buzali/SuperListas/Firmware/SL App/LCD.c

/*********************************************************************
 *
 *                  LCD.c
 * 
*********************************************************************/

#include "HardwareProfile.h"
#include "Dogm/utility/dogm128.h"
#include <libpic30.h>
#include "LCD.h"
#include <stdlib.h>

//SuperListas Logo
const unsigned char logo_win [] = {
0x00, 0x00, 0x00, 0x00, 0x00, 0x00, 0x00, 0x00, 0x00, 0x00, 0x00, 0x00, 0x00, 0x00, 0x00, 0x00,
0x00, 0x00, 0x00, 0x00, 0x00, 0x00, 0x00, 0x00, 0x00, 0x00, 0x00, 0x00, 0x00, 0x00, 0x00, 0x00,
0x00, 0x00, 0x00, 0x00, 0x00, 0x00, 0x00, 0x00, 0x00, 0x00, 0x00, 0x00, 0x00, 0x00, 0x00, 0x00,
0x07, 0x00, 0x00, 0x00, 0x00, 0x00, 0x00, 0x00, 0x00, 0x00, 0x00, 0x00, 0x00, 0x00, 0x00, 0x00,
0x3F, 0xE0, 0x00, 0x00, 0x00, 0x00, 0x00, 0x00, 0x38, 0x00, 0xE0, 0x00, 0x04, 0x00, 0x00, 0x00,
0x7F, 0xF0, 0x00, 0x00, 0x00, 0x00, 0x00, 0x00, 0x38, 0x00, 0xE0, 0x00, 0x1C, 0x00, 0x00, 0x00,
0x78, 0xF0, 0x00, 0x00, 0x00, 0x00, 0x00, 0x00, 0x38, 0x00, 0x00, 0x00, 0x1C, 0x00, 0x00, 0x00,
0x70, 0x78, 0x00, 0x00, 0x00, 0x00, 0x00, 0x00, 0x38, 0x00, 0x00, 0x00, 0x1C, 0x00, 0x00, 0x00,
0x70, 0x00, 0xE1, 0xC3, 0x3E, 0x03, 0xE0, 0x6F, 0x38, 0x00, 0xE1, 0xFC, 0x7F, 0x0F, 0xE0, 0xFE,
0x7C, 0x00, 0xE1, 0xC3, 0xFF, 0x0F, 0xF0, 0x7F, 0x38, 0x00, 0xE3, 0xFE, 0x7F, 0x1F, 0xF1, 0xFF,
0x7F, 0xC0, 0xE1, 0xC3, 0xEF, 0x0F, 0x78, 0x7E, 0x38, 0x00, 0xE3, 0x8E, 0x3F, 0x3C, 0xF1, 0xC7,
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
            //primera[fila]
        word = strtok(NULL, delim);
    }
    int i;
    i=0;

    //LCD_printMultilinea(primera, fila);
  dog_StartPage();
  do{
    for (i=0; i<=fila ;i++){
    dog_DrawStr(0, 52- c_height*i, font_6x13, primera[i]);
    }
  } while( dog_NextPage() );

}
