buzali/SuperListas/Firmware/SL App/LCD.h

/*********************************************************************
 *
 *                  Headers for LCD
*********************************************************************/

void LCD_printLogo(void);
void LCD_init(void);
void LCD_printSTR(const char *s);
