buzali/SuperListas/Web Application/superlistas/upc/admin.py

from django.contrib import admin
from models import *

admin.site.register(Usuario)
admin.site.register(Producto)
admin.site.register(Familia)
admin.site.register(Lista)
admin.site.register(Seleccionado)
