buzali/SuperListas/Firmware/SL App/Dogm/utility/dogmspi.c

/*

  dogmspi.c
  
  (c) 2010 Oliver Kraus (olikraus@gmail.com)
  
  spi abstraction layer
  
  This file is part of the dogm128 library.

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

  ST7565R SPI interface
  
    ST7565R reads data with rising edge of the clock signal (SCL)
      --> CPHA = 0 and CPOL = 0
    ST7565R reads  MSB first 
      --> DORD = 0
      
  /usr/lib/avr/include/avr/pgmspace.h
  
  
  This file is controlled by the following defines:
  
  DOG_SPI_USI
    --> ATTINY 
  DOG_SPI_ATMEGA
    --> ATMEGA
  DOG_SPI_SW_ARDUINO
      --> default for ADA_ST7565P_HW
  DOG_SPI_ARDUINO or "nothing defined"
    --> Arduino 
  DOG_SPI_SW_STD_ARDUINO
  
  DOG_SPI_CHIPKIT_PIC32

*/

#ifndef BETA_2
#include "dogm128.h"

#if defined(DOG_SPI_USI)
#elif defined(DOG_SPI_ATMEGA)
#elif defined(DOG_SPI_ARDUINO)
#elif defined(DOG_SPI_SW_ARDUINO)
#elif defined(DOG_SPI_CHIPKIT_PIC32)
#elif defined(DOG_SPI_SW_STD_ARDUINO)
#else  /* nothing defined */
#if defined(ADA_ST7565P_HW) || defined(__AVR_ATmega1280__) || defined(__AVR_ATmega2560__)
#define DOG_SPI_SW_ARDUINO
#elif defined(__18CXX) || defined(__PIC32MX)
#define DOG_SPI_CHIPKIT_PIC32
//#define DOG_SPI_SW_STD_ARDUINO
#else
#define DOG_SPI_ARDUINO
#endif
#endif


#if defined(DOG_SPI_USI)

/*=======================================================================*/
/* USI Interface */
/*=======================================================================*/

#include <avr/interrupt.h>
#include <avr/io.h>
#include <util/delay.h>

#define _DOG_SPI_DDR(PCHAR) DDR ## PCHAR
#define DOG_SPI_DDR(PCHAR) _DOG_SPI_DDR(PCHAR)
#define _DOG_SPI_PORT(PCHAR) PORT ## PCHAR
#define DOG_SPI_PORT(PCHAR) _DOG_SPI_PORT(PCHAR)

/* dog_spi_pin_a0 is ignored, instead, port and pins are hard coded */
#ifndef DOG_SPI_SCL_PORT
#define DOG_SPI_SCL_PORT A
#warning DOG_SPI_SCL_PORT not defined, port A assumed
#endif
#ifndef DOG_SPI_SCL_PIN
#define DOG_SPI_SCL_PIN 4
#warning DOG_SPI_SCL_PIN not defined, bit 4 assumed
#endif


#ifndef DOG_SPI_DO_PORT
#define DOG_SPI_DO_PORT A
#warning DOG_SPI_DO_PORT not defined, port A assumed
#endif 

#ifndef DOG_SPI_DO_PIN
#define DOG_SPI_DO_PIN 5
#warning DOG_SPI_DO_PIN not defined, bit 5 assumed
#endif 

#ifndef DOG_SPI_CS_PORT
#define DOG_SPI_CS_PORT B
#warning DOG_SPI_CS_PORT not defined, port B assumed
#endif 

#ifndef DOG_SPI_CS_PIN
#define DOG_SPI_CS_PIN 0
#warning DOG_SPI_CS_PIN not defined, bit 0 assumed
#endif 

#ifndef DOG_SPI_A0_PORT
#define DOG_SPI_A0_PORT B
#warning DOG_SPI_A0_PORT not defined, port B assumed
#endif 

#ifndef DOG_SPI_A0_PIN
#define DOG_SPI_A0_PIN 1
#warning DOG_SPI_A0_PIN not defined, bit 1 assumed
#endif 

void dog_spi_init(void)
{
  /* setup port directions */
  DOG_SPI_DDR(DOG_SPI_CS_PORT) |= _BV(DOG_SPI_CS_PIN);
  DOG_SPI_DDR(DOG_SPI_DO_PORT) |= _BV(DOG_SPI_DO_PIN);
  DOG_SPI_DDR(DOG_SPI_A0_PORT) |= _BV(DOG_SPI_A0_PIN);
  /* DOG_SPI_SCL_DDR |= _BV(DOG_SPI_SCL_PIN); */
  DOG_SPI_DDR(DOG_SPI_SCL_PORT) |= _BV(DOG_SPI_SCL_PIN);
}

unsigned char dog_spi_out(unsigned char data)
{
  uint8_t i = 8;
  /* the SCL level is set during dog_spi_enable_client() */
  /* output the data */
  USIDR = data;
  do
  {
    /* generate edge at the clock pin, edge types depends of the current pin state */
    /* slave should now sample the data */
    USICR = _BV(USIWM0) | _BV(USITC);
    /* output next bit and toggle the clock pin again*/
    USICR = _BV(USIWM0) | _BV(USICLK) | _BV(USITC);
    i--;
  } while( i != 0 );  
  return USIDR;
}

void dog_spi_enable_client(void)
{
  /* before the slave is enabled, esure that the clk pin has a logical zero */
  DOG_SPI_PORT(DOG_SPI_SCL_PORT) &= ~_BV(DOG_SPI_SCL_PIN);
  
  /* now enable the SPI slave */
  DOG_SPI_PORT(DOG_SPI_CS_PORT) &= ~_BV(DOG_SPI_CS_PIN);
}

void dog_spi_disable_client(void)
{
  /* disable the client (write a logical zero on the CS line) */
  DOG_SPI_PORT(DOG_SPI_CS_PORT) |= _BV(DOG_SPI_CS_PIN);
}

void dog_cmd_mode(void)
{
  DOG_SPI_PORT(DOG_SPI_A0_PORT) &= ~_BV(DOG_SPI_A0_PIN);
}

void dog_data_mode(void)
{
  DOG_SPI_PORT(DOG_SPI_A0_PORT) |= _BV(DOG_SPI_A0_PIN);
}

#elif defined(DOG_SPI_ATMEGA)

/*=======================================================================*/
/* SPI Interface of ATMEGA */
/*=======================================================================*/

#include <avr/interrupt.h>
#include <avr/io.h>
#include <util/delay.h>

#define _DOG_SPI_DDR(PCHAR) DDR ## PCHAR
#define DOG_SPI_DDR(PCHAR) _DOG_SPI_DDR(PCHAR)
#define _DOG_SPI_PORT(PCHAR) PORT ## PCHAR
#define DOG_SPI_PORT(PCHAR) _DOG_SPI_PORT(PCHAR)

/* dog_spi_pin_a0 is ignored, instead, port and pins are hard coded */
#ifndef DOG_SPI_SCL_PORT
#define DOG_SPI_SCL_PORT B
#warning DOG_SPI_SCL_PORT not defined, port B assumed
#endif
#ifndef DOG_SPI_SCL_PIN
#define DOG_SPI_SCL_PIN 5
#warning DOG_SPI_SCL_PIN not defined, bit 5 assumed
#endif


#ifndef DOG_SPI_MOSI_PORT
#define DOG_SPI_MOSI_PORT B
#warning DOG_SPI_MOSI_PORT not defined, port B assumed
#endif 

#ifndef DOG_SPI_MOSI_PIN
#define DOG_SPI_MOSI_PIN 3
#warning DOG_SPI_MOSI_PIN not defined, bit 3 assumed
#endif 

#ifndef DOG_SPI_A0_PORT
#define DOG_SPI_A0_PORT B
#warning DOG_SPI_A0_PORT not defined, port B assumed
#endif 

#ifndef DOG_SPI_A0_PIN
#define DOG_SPI_A0_PIN 1
#warning DOG_SPI_A0_PIN not defined, bit 1 assumed
#endif 

#ifndef DOG_SPI_SS_PORT
#define DOG_SPI_SS_PORT B
#warning DOG_SPI_SS_PORT not defined, port B assumed
#endif 

#ifndef DOG_SPI_SS_PIN
#define DOG_SPI_SS_PIN 2
#warning DOG_SPI_SS_PIN not defined, bit 2 assumed
#endif 

void dog_spi_init(void)
{
  /* NOTE: SS Pin must be set to output, otherwise the SPI system might assume a collision */
  
  /* setup port directions */
  DOG_SPI_DDR(DOG_SPI_MOSI_PORT) |= _BV(DOG_SPI_MOSI_PIN);
  DOG_SPI_DDR(DOG_SPI_A0_PORT) |= _BV(DOG_SPI_A0_PIN);
  DOG_SPI_DDR(DOG_SPI_SCL_PORT) |= _BV(DOG_SPI_SCL_PIN);
  DOG_SPI_DDR(DOG_SPI_SS_PORT) |= _BV(DOG_SPI_SS_PIN);
  
    /*
    SPR1 SPR0
	0	0		fclk/4
	0	1		fclk/16
	1	0		fclk/64
	1	1		fclk/128
  */
  
  
  
  SPCR = 0;
  SPCR =  (1<<SPE) | (1<<MSTR)|(0<<SPR1)|(0<<SPR0)|(0<<CPOL)|(0<<CPHA);
}

unsigned char dog_spi_out(unsigned char data)
{
  /* send data */
  SPDR = data;
  /* wait for transmission */
  while (!(SPSR & (1<<SPIF))) 
    ;
  /* clear the SPIF flag by reading SPDR */
  //dog_Delay(1);
  return  SPDR;
  //return data;
}

void dog_spi_enable_client(void)
{
  /* before the slave is enabled, esure that the clk pin has a logical zero */
  DOG_SPI_PORT(DOG_SPI_SCL_PORT) &= ~_BV(DOG_SPI_SCL_PIN);
  
  /* now enable the SPI slave */
  DOG_SPI_PORT(DOG_SPI_SS_PORT) &= ~_BV(DOG_SPI_SS_PIN);
}

void dog_spi_disable_client(void)
{
  /* disable the client (write a logical zero on the CS line) */
  DOG_SPI_PORT(DOG_SPI_SS_PORT) |= _BV(DOG_SPI_SS_PIN);
}

void dog_cmd_mode(void)
{
  DOG_SPI_PORT(DOG_SPI_A0_PORT) &= ~_BV(DOG_SPI_A0_PIN);
}

void dog_data_mode(void)
{
  DOG_SPI_PORT(DOG_SPI_A0_PORT) |= _BV(DOG_SPI_A0_PIN);
}



#elif defined(__18CXX)

/*=======================================================================*/
/* Microchip PIC18 SPI */
/*=======================================================================*/
#include <p18cxxx.h>

#define LCD_A0_TRIS		(TRISCbits.TRISC1)
#define LCD_A0_IO		(LATCbits.LATC1)
#define LCD_CS_TRIS		(TRISCbits.TRISC2)
#define LCD_CS_IO		(LATCbits.LATC2)

#define LCD_CLK_TRIS	(TRISCbits.TRISC3)
#define LCD_SDO_TRIS	(TRISCbits.TRISC5)
#define LCD_SDI_TRIS	(TRISCbits.TRISC4) // remove it!!!!
#define LCD_SPI_IF		(PIR1bits.SSPIF)
#define LCD_SSPBUF		(SSPBUF)
#define LCD_SPICON1		(SSPCON1)
#define LCD_SPICON1bits	(SSPCON1bits)
#define LCD_SPICON2		(SSPCON2)
#define LCD_SPISTAT		(SSPSTAT)
#define LCD_SPISTATbits	(SSPSTATbits)
#define LCD_SPI_ON_BIT  (LCD_SPICON1bits.SSPEN)
#define WaitForDataByte()   do{while(!LCD_SPI_IF); LCD_SPI_IF = 0;}while(0)


void dog_spi_init(void)
{
	LCD_CS_IO=1;
	LCD_A0_IO=1;

	LCD_A0_TRIS=0;
	LCD_CS_TRIS =0;

	LCD_CLK_TRIS =0;
	LCD_SDO_TRIS =0;
	LCD_SDI_TRIS =1;

	SSPSTAT=0x40;
	SSPCON1=0x21;

	PIR1bits.SSPIF=0;
}

unsigned char dog_spi_out(unsigned char data)
{
  		volatile uint8_t vDummy;
		LCD_SSPBUF=data;
		//     while (LCD_SPISTATbits.SPITBF == 1);
		WaitForDataByte();
		//LCD_SPI_IF=0;
		vDummy = LCD_SSPBUF;

}

void dog_spi_enable_client(void)
{
LCD_CS_IO=0;
}

void dog_spi_disable_client(void)
{
  LCD_CS_IO=1;
}

void dog_cmd_mode(void)
{
  LCD_A0_IO=0;
}

void dog_data_mode(void)
{
  LCD_A0_IO=1;
}

#elif defined(DOG_SPI_ARDUINO)

/*=======================================================================*/
/* Arduino SPI */
/*=======================================================================*/


#include <avr/interrupt.h>
#include <avr/io.h>
#include <util/delay.h>
#include <wiring.h>	/* arduino pinMode */

void dog_spi_init(void)
{
  pinMode(PIN_SCK, OUTPUT);
  pinMode(PIN_MOSI, OUTPUT);
  /* pinMode(PIN_MISO, INPUT); */

  // This this redundant with dog_spi_pin_cs... 
  // pinMode(PIN_SS, OUTPUT);			/* this must always be an output port */

  pinMode(dog_spi_pin_a0, OUTPUT);
  pinMode(dog_spi_pin_cs, OUTPUT);			/* this is the user chip select */

  /*
    SPR1 SPR0
	0	0		fclk/4
	0	1		fclk/16
	1	0		fclk/64
	1	1		fclk/128
  */
  SPCR = 0;
  SPCR =  (1<<SPE) | (1<<MSTR)|(0<<SPR1)|(0<<SPR0)|(0<<CPOL)|(0<<CPHA);
  /*
  {
  unsigned char x;
    x = SPSR;
    x= SPDR;
  }
  */
}

unsigned char dog_spi_out(unsigned char data)
{
  /* unsigned char x = 100; */
  /* send data */
  SPDR = data;
  /* wait for transmission */
  while (!(SPSR & (1<<SPIF))) 
    ;
  /* clear the SPIF flag by reading SPDR */
  return  SPDR;
}

void dog_spi_enable_client(void)
{
  digitalWrite(PIN_SCK, LOW);
  digitalWrite(dog_spi_pin_cs, LOW);  
}

void dog_spi_disable_client(void)
{
  digitalWrite(dog_spi_pin_cs, HIGH);
}

void dog_cmd_mode(void)
{
  digitalWrite(dog_spi_pin_a0, LOW);
}

void dog_data_mode(void)
{
  digitalWrite(dog_spi_pin_a0, HIGH);
}

#elif defined(DOG_SPI_SW_ARDUINO)

/*=======================================================================*/
/* Arduino Software SPI */
/*=======================================================================*/

/*
  fast shift out
    - interface compatible with shiftOut
  restrictions (compared to shiftOut)
    - PWM is not deactivated for the digital pins: Ensure that PWM is not active for both pins
    - Port is not set as output for both pins. This must be done before calling shiftOutFast.

  Performance Test DOGM128 Library, Arduino Uno, DOGS102 Display, SpaceTrash Example
    DOUBLE_MEM, shiftOut:		9 FPS (frames per second)
    DOUBLE_MEM, shiftOutFast:	31 FPS
    DOUBLE_MEM, Hardware SPI:	42 FPS
  
*/
#include "wiring_private.h"
#include "pins_arduino.h"


uint8_t dog_bitData, dog_bitNotData;
uint8_t dog_bitClock, dog_bitNotClock;
volatile uint8_t *dog_outData;
volatile uint8_t *dog_outClock;

void dog_init_shift_out(uint8_t dataPin, uint8_t clockPin)
{
  dog_outData = portOutputRegister(digitalPinToPort(dataPin));
  dog_outClock = portOutputRegister(digitalPinToPort(clockPin));
  dog_bitData = digitalPinToBitMask(dataPin);
  dog_bitClock = digitalPinToBitMask(clockPin);

  dog_bitNotClock = dog_bitClock;
  dog_bitNotClock ^= 0x0ff;

  dog_bitNotData = dog_bitData;
  dog_bitNotData ^= 0x0ff;
}

void dog_do_shift_out_msb_first(uint8_t val)
{
  uint8_t cnt = 8;
  uint8_t bitData = dog_bitData;
  uint8_t bitNotData = dog_bitNotData;
  uint8_t bitClock = dog_bitClock;
  uint8_t bitNotClock = dog_bitNotClock;
  volatile uint8_t *outData = dog_outData;
  volatile uint8_t *outClock = dog_outClock;
  do
  {
    if ( val & 128 )
      *outData |= bitData;
    else
      *outData &= bitNotData;
    
    *outClock |= bitClock;
    *outClock &= bitNotClock;
    val <<= 1;
    cnt--;
  } while( cnt != 0 );
}

#ifdef __AVR__
#include <avr/interrupt.h>
#include <avr/io.h>
#include <util/delay.h>
#endif

#include <wiring.h>	/* arduino pinMode */

void dog_spi_init(void)
{
  pinMode(PIN_SCK, OUTPUT);
  digitalWrite(PIN_SCK, LOW);
  pinMode(PIN_MOSI, OUTPUT);
  digitalWrite(PIN_MOSI, LOW);
  pinMode(dog_spi_pin_a0, OUTPUT);
  if (dog_spi_pin_cs > 0)
  {
    pinMode(dog_spi_pin_cs, OUTPUT);			/* this is the user chip select */
    digitalWrite(dog_spi_pin_cs, HIGH);
  }

#ifdef ADA_ST7565P_HW  
  // Reset procedure taken from Adafruit ST7565 library
  // toggle RST low to reset; CS low so it'll listen to us
  if ( dog_spi_pin_rst > 0 )
  {
    pinMode(dog_spi_pin_rst, OUTPUT);
    digitalWrite(dog_spi_pin_rst, LOW);
    dog_Delay(100);
    digitalWrite(dog_spi_pin_rst, HIGH);
    dog_Delay(10);
  }
#endif
  dog_init_shift_out(PIN_MOSI, PIN_SCK);
}



unsigned char dog_spi_out(unsigned char data)
{
  //shiftOutFast(PIN_MOSI, PIN_SCK, MSBFIRST, data);
  dog_do_shift_out_msb_first(data);
  return data;
}

void dog_spi_enable_client(void)
{
  digitalWrite(PIN_SCK, LOW);
  digitalWrite(dog_spi_pin_cs, LOW);  
}

void dog_spi_disable_client(void)
{
  digitalWrite(dog_spi_pin_cs, HIGH);
}

void dog_cmd_mode(void)
{
  digitalWrite(dog_spi_pin_a0, LOW);
}

void dog_data_mode(void)
{
  digitalWrite(dog_spi_pin_a0, HIGH);
}

#elif defined(DOG_SPI_CHIPKIT_PIC32)

/*=======================================================================*/
/* CHIPKIT Software SPI */
/*=======================================================================*/

#include <wiring.h>	/* arduino pinMode */

#include "wiring_private.h"
#include "pins_arduino.h"


uint16_t dog_bitData, dog_bitNotData;
uint16_t dog_bitClock, dog_bitNotClock;
volatile uint32_t *dog_outData;
volatile uint32_t *dog_outClock;
volatile uint32_t dog_pic32_spi_tmp;

void dog_init_shift_out(uint8_t dataPin, uint8_t clockPin)
{
  dog_outData = portOutputRegister(digitalPinToPort(dataPin));
  dog_outClock = portOutputRegister(digitalPinToPort(clockPin));
  dog_bitData = digitalPinToBitMask(dataPin);
  dog_bitClock = digitalPinToBitMask(clockPin);

  dog_bitNotClock = dog_bitClock;
  dog_bitNotClock ^= 0x0ffff;

  dog_bitNotData = dog_bitData;
  dog_bitNotData ^= 0x0ffff;
}

void dog_do_shift_out_msb_first(uint8_t val)
{
  uint8_t cnt = 8;
  do
  {
    if ( val & 128 )
	*dog_outData |= dog_bitData;
    else
	*dog_outData &= dog_bitNotData;    
    val <<= 1;
    /*
	There must be some delay here. However
	fetching the adress dog_outClock is enough delay, so
	do not place dog_outClock in a local variable. This will
	break the procedure
    */
    *dog_outClock |= dog_bitClock;
    cnt--;
    *dog_outClock &= dog_bitNotClock;
    /* 
	little additional delay after clk pulse, done by 3x32bit reads 
	from I/O. Optimized for PIC32 with 80 MHz.
    */
    dog_pic32_spi_tmp = *dog_outClock;
    dog_pic32_spi_tmp = *dog_outClock;
    dog_pic32_spi_tmp = *dog_outClock;
  } while( cnt != 0 );
}

void dog_spi_init(void)
{
  pinMode(PIN_SCK, OUTPUT);
  digitalWrite(PIN_SCK, LOW);
  pinMode(PIN_MOSI, OUTPUT);
  digitalWrite(PIN_MOSI, LOW);
  pinMode(PIN_A0_DEFAULT, OUTPUT); 
  pinMode(PIN_SS, OUTPUT);			/* this is the user chip select */
  digitalWrite(PIN_SS, HIGH);
  dog_init_shift_out(PIN_MOSI, PIN_SCK);
  dog_Delay(1);
}

unsigned char dog_spi_out(unsigned char data)
{
  dog_do_shift_out_msb_first(data);
  return data;
}

void dog_spi_enable_client(void)
{
  digitalWrite(PIN_SCK, LOW);
  digitalWrite(PIN_SS, LOW);  
}

void dog_spi_disable_client(void)
{
   digitalWrite(PIN_SS, HIGH);
}

void dog_cmd_mode(void)
{
  digitalWrite(PIN_A0_DEFAULT, LOW);
}

void dog_data_mode(void)
{
  digitalWrite(PIN_A0_DEFAULT, HIGH);
}

#elif defined(DOG_SPI_SW_STD_ARDUINO)

/*=======================================================================*/
/* Arduino Software SPI with standard procedures, should work for CHIPKIT */
/*=======================================================================*/

#include <wiring.h>	/* arduino pinMode */

void myShiftOut(uint8_t dataPin, uint8_t clockPin, uint8_t val)
{
  uint8_t i = 8;
  do
  {
    if ( val & 128 )
      digitalWrite(dataPin, HIGH);
    else
      digitalWrite(dataPin, LOW);
    val <<= 1;
    digitalWrite(clockPin, HIGH);
    digitalWrite(clockPin, LOW);		
    i--;
  } while( i != 0 );
}

void dog_spi_init(void)
{
  pinMode(PIN_SCK, OUTPUT);
  digitalWrite(PIN_SCK, LOW);
  pinMode(PIN_MOSI, OUTPUT);
  digitalWrite(PIN_MOSI, LOW);
  pinMode(PIN_A0_DEFAULT, OUTPUT); 
  pinMode(PIN_SS, OUTPUT);			/* this is the user chip select */
  digitalWrite(PIN_SS, HIGH);
  dog_Delay(1);
}

unsigned char dog_spi_out(unsigned char data)
{
  myShiftOut(PIN_MOSI, PIN_SCK, data);
  return data;
}

void dog_spi_enable_client(void)
{
  digitalWrite(PIN_SCK, LOW);
  digitalWrite(PIN_SS, LOW);  
}

void dog_spi_disable_client(void)
{
   digitalWrite(PIN_SS, HIGH);
}

void dog_cmd_mode(void)
{
  digitalWrite(PIN_A0_DEFAULT, LOW);
  //dog_Delay(1);
}

void dog_data_mode(void)
{
  digitalWrite(PIN_A0_DEFAULT, HIGH);
  //dog_Delay(1);
}

#endif

#endif
