buzali/SuperListas/Firmware/SL App/M2tklib/utility/m2key.c

/*

  m2key.c

  key debounce and queue

  m2tklib = Mini Interative Interface Toolkit Library
  
  Copyright (C) 2011  olikraus@gmail.com

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
*/

#include "m2.h"
#define FCY 4900000
#include <libpic30.h>


#define M2_DEBOUNCE_CNT 3

uint8_t m2_GetKeyFromQueue(m2_p m2)
{
  uint8_t key;
  if ( m2->key_queue_len == 0 )
    return M2_KEY_NONE;
  
  {  
#ifdef __AVR__
    uint8_t status_reg = SREG;
    cli();
#endif

    key = m2->key_queue_array[m2->key_queue_pos];
    m2->key_queue_pos++;
    m2->key_queue_pos &= (M2_KEY_QUEUE_LEN-1);
    m2->key_queue_len--;
    
#ifdef __AVR__
    SREG = status_reg;
#endif
  }
  return key;
}

void m2_PutKeyIntoQueue(m2_p m2, uint8_t key_code)
{
  uint8_t pos;
  
  if ( key_code == M2_KEY_NONE )
    return;

  {  
#ifdef __AVR__
    uint8_t status_reg = SREG;
    cli();
#endif

    pos = m2->key_queue_pos;
    pos += m2->key_queue_len;
    pos &= (M2_KEY_QUEUE_LEN-1);
    m2->key_queue_array[pos] = key_code;
    
    if ( m2->key_queue_len >= M2_KEY_QUEUE_LEN ) 
      m2->key_queue_pos++;
    else
      m2->key_queue_len++;
    
#ifdef __AVR__
    SREG = status_reg;
#endif
  }
}


/*
  debounce key and put key into queue
*/
void m2_SetDetectedKey(m2_p m2, uint8_t key_code)
{
  
  /* if event source has set the EVENT bit, then directly pass this value to the queue */
  
  if ( M2_IS_KEY_EVENT(key_code) )
  {
    key_code &= ~M2_KEY_EVENT_MASK;
    m2_PutKeyIntoQueue(m2, key_code);
    return;
  }
  
  /* debounce the value */
  /*
    state machine
    Input: key_code
  
    A (reset): no keys detected
	if key_code == NONE, stay in A
	if key_code != NONE, then: reset counter & detected_key_code = key_code & goto B
  
    B: button down wait
	if detected_key_code != key_code goto A
	if counter == 0 then BUTTON PRESSED goto C
	Else counter--, stay in B
  
    C: button pressed, wait for release
	if key_code == NONE goto, reset counter D
	if detected_key_code == key_code stay in C
	if detected_key_code != key_code goto A
    
    D: wait for button release
	if counter == 0 then BUTTON RELEASE goto A 
	if  key_code == NONE then counter--, stay in D
	if detected_key_code == key_code goto C
	if detected_key_code != key_code goto A
	
  */
  
  switch(m2->debounce_state)
  {
    case M2_DEBOUNCE_STATE_WAIT_FOR_KEY_PRESS:
      if ( key_code != M2_KEY_NONE )
      {
	m2->detected_key_timer = M2_DEBOUNCE_CNT;
	m2->detected_key_code = key_code;
	m2->debounce_state = M2_DEBOUNCE_STATE_PRESS;
      }
      break;
    case M2_DEBOUNCE_STATE_PRESS:
      if ( m2->detected_key_code != key_code )
      {
	m2->debounce_state = M2_DEBOUNCE_STATE_WAIT_FOR_KEY_PRESS;
      }
      else if ( m2->detected_key_timer == 0 )
      {
	m2->debounce_state = M2_DEBOUNCE_STATE_WAIT_FOR_KEY_RELEASE;
      }
      else
      {
	m2->detected_key_timer--;
      }
      break;
    case M2_DEBOUNCE_STATE_WAIT_FOR_KEY_RELEASE:
      if ( key_code == M2_KEY_NONE )
      {
	m2->detected_key_timer = M2_DEBOUNCE_CNT;
	m2->debounce_state = M2_DEBOUNCE_STATE_RELEASE;
      }
      else if ( m2->detected_key_code != key_code )
      {
	m2->debounce_state = M2_DEBOUNCE_STATE_WAIT_FOR_KEY_PRESS;
      }      
      break;
    case M2_DEBOUNCE_STATE_RELEASE:
      if ( m2->detected_key_code == key_code )
      {
	m2->debounce_state = M2_DEBOUNCE_STATE_WAIT_FOR_KEY_RELEASE;
      }
      else if ( m2->detected_key_timer == 0 )
      { 
	m2->debounce_state = M2_DEBOUNCE_STATE_WAIT_FOR_KEY_PRESS;
	m2_PutKeyIntoQueue(m2, m2->detected_key_code);
      }
      else if ( key_code != M2_KEY_NONE && m2->detected_key_code != key_code )
      {
	m2->debounce_state = M2_DEBOUNCE_STATE_WAIT_FOR_KEY_PRESS;
      }
      else
      {
	m2->detected_key_timer--;
      }
      break;
  }  
}
