buzali/SuperListas/Firmware/SL App/M2tklib/utility/m2obj.c

/*
  m2obj.c
  
  m2tklib = Mini Interative Interface Toolkit Library
  
  Copyright (C) 2011  olikraus@gmail.com

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

  
  Simplified Top Level API of the m2tklib.
  Most important: Init and event processing  
  - read keys 
  - pass key values to the event handler
  
  
  
*/

#include "m2.h"

void m2_SetEventSourceHandlerM2(m2_p m2, m2_es_fnptr es)
{
  if ( es != NULL )
  {
    m2->es = es;
    m2->es(m2, M2_ES_MSG_INIT);
  }
}

void m2_SetGraphicsHandlerM2(m2_p m2, m2_gfx_fnptr gh)
{
  if ( gh != NULL )
  {
    m2->gh = gh;
    m2_PutKeyIntoQueue(m2, M2_KEY_REFRESH);
  }
}

/*
  element: 	the root element
  es:			event source handler, can be NULL
  eh:			event handler to process the source events
  gh:			graphics handler
*/
void m2_InitM2(m2_p m2, m2_rom_void_p element, m2_es_fnptr es, m2_eh_fnptr eh, m2_gfx_fnptr gh)
{
  m2->is_frame_draw_at_end = 0;
  m2->key_queue_len = 0;
  m2->key_queue_pos = 0;
  m2->eh = eh;
  m2->gh = gh;
  m2_gfx_init(gh);
  m2->is_frame_draw_at_end = m2_gfx_is_frame_draw_at_end();
  m2->forced_key = M2_KEY_REFRESH;
  m2->debounce_state = M2_DEBOUNCE_STATE_WAIT_FOR_KEY_PRESS;
  m2_PutKeyIntoQueue(m2, M2_KEY_REFRESH);
  m2_nav_init(m2_get_nav(m2),  element);
  m2_SetEventSourceHandlerM2(m2, es);
}

void m2_CheckKeyM2(m2_p m2)
{
  uint8_t key;
  
  /* step 1: get raw key */
  
  /* check if a key should be forced */
  /* obsolete
  key = m2->forced_key;
  if ( key != M2_KEY_NONE )
  {
    m2->forced_key = M2_KEY_NONE;
    m2_PutKeyIntoQueue(m2, key);
  }
  else
  */
  {
    /* request key information from the event source */
    if ( m2->es != NULL )
    {
      key = m2->es(m2, M2_ES_MSG_GET_KEY);
      //m2_PutKeyIntoQueue(m2, key);
      m2_SetDetectedKey(m2, key);
    }
    else
      key = M2_KEY_NONE;
  }
}


/*
  return:
    0: nothing happend
    1:	event has been processed
*/
uint8_t m2_HandleKeyM2(m2_p m2)
{
  uint8_t is_redraw_required = 0;
  uint8_t key;
  
  if ( m2_nav_check_and_assign_new_root(m2_get_nav(m2)) != 0 )
    return 1;	/* break and let redraw */
  
  if ( m2_GetRootM2(m2) == &m2_null_element )
    return 0;
  
  for(;;)
  {
    /* check if the root node has been changed */
    if ( m2_nav_check_and_assign_new_root(m2_get_nav(m2)) != 0 )
      return 1;	/* break and let redraw */

    key = m2_GetKeyFromQueue(m2);
    
    /* if there are no more keys, break out of the loop */
    if ( key == M2_KEY_NONE )
      break;
    
    /* otherwise, process the key event */
    /* note, that key numbers are equal to message numbers */
    if ( m2->eh != NULL )
    {
      /* handle the key */
      m2->eh(m2, key, 0);
    }
    
    is_redraw_required = 1;
  }
  
  return is_redraw_required;
}

void m2_SetFontM2(m2_p m2, uint8_t font_idx, const void *font_ptr)
{
  m2_gfx_set_font(m2->gh, font_idx, font_ptr);
  m2_PutKeyIntoQueue(m2, M2_KEY_REFRESH);
}

void m2_SetRootM2(m2_p m2, m2_rom_void_p element)
{
  m2_nav_set_root(m2_get_nav(m2),  element);
}

m2_rom_void_p m2_GetRootM2(m2_p m2)
{
  return m2_get_nav(m2)->element_list[0];
}

void m2_ClearM2(m2_p m2)
{
  m2_SetRootM2(m2, NULL);
}
